gojimmypi/ulx3s-elecrow-7inch-hdmi-enclosure/images/A1-A1-connector-size.jpg

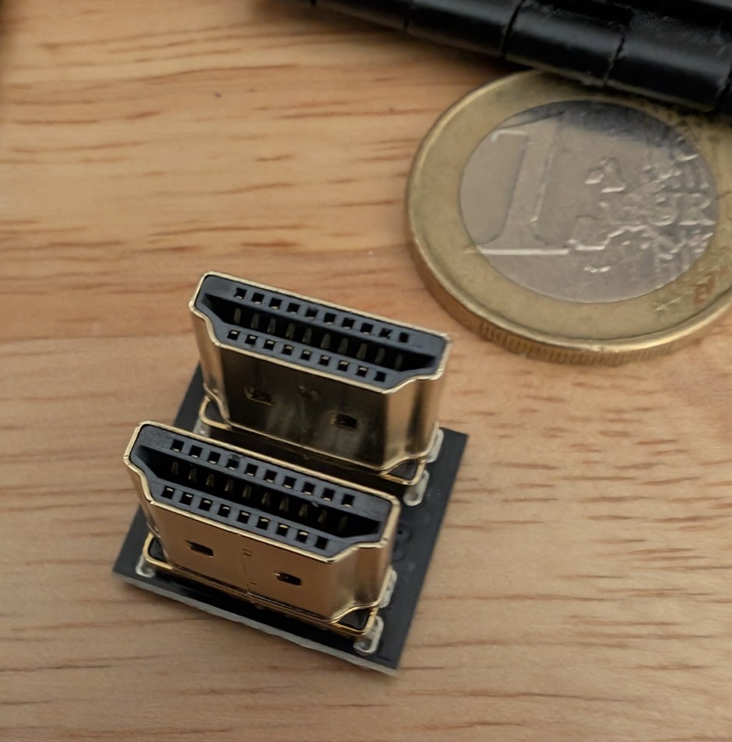
images/A1-A1-connector-size.jpg
