gojimmypi/ulx3s-elecrow-7inch-hdmi-enclosure/images/creality_filament_tangle.jpg

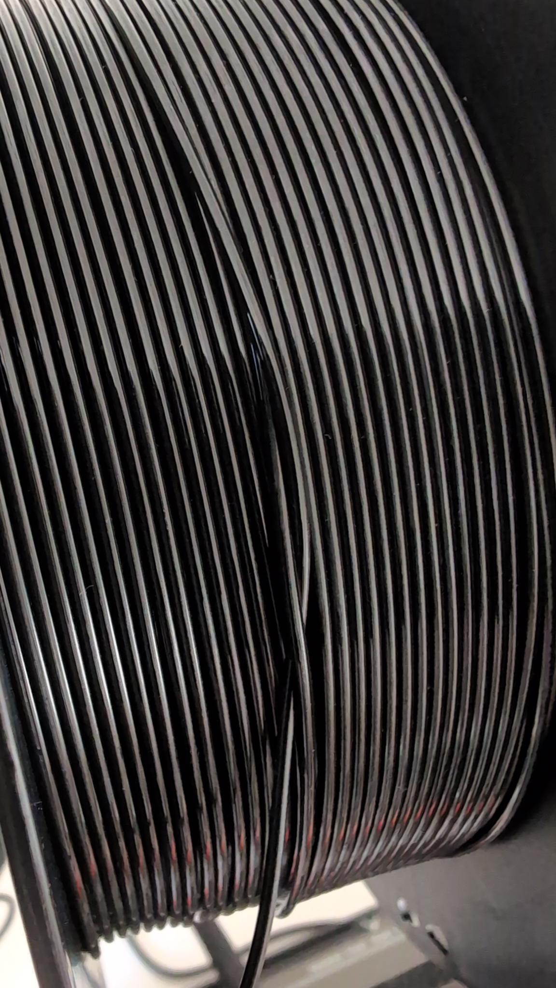
images/creality_filament_tangle.jpg
