gojimmypi/ulx3s-elecrow-7inch-hdmi-enclosure/images/creality_support_reply.jpg

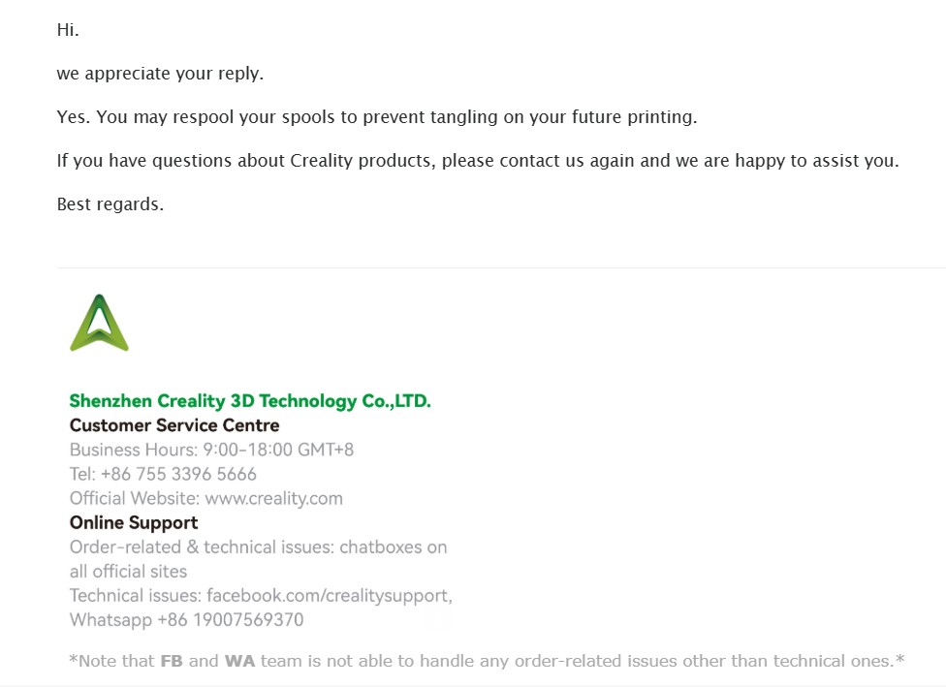
images/creality_support_reply.jpg
