gojimmypi/ulx3s-elecrow-7inch-hdmi-enclosure/images/Elecrow-7inch-HMDI-dimensions.jpg

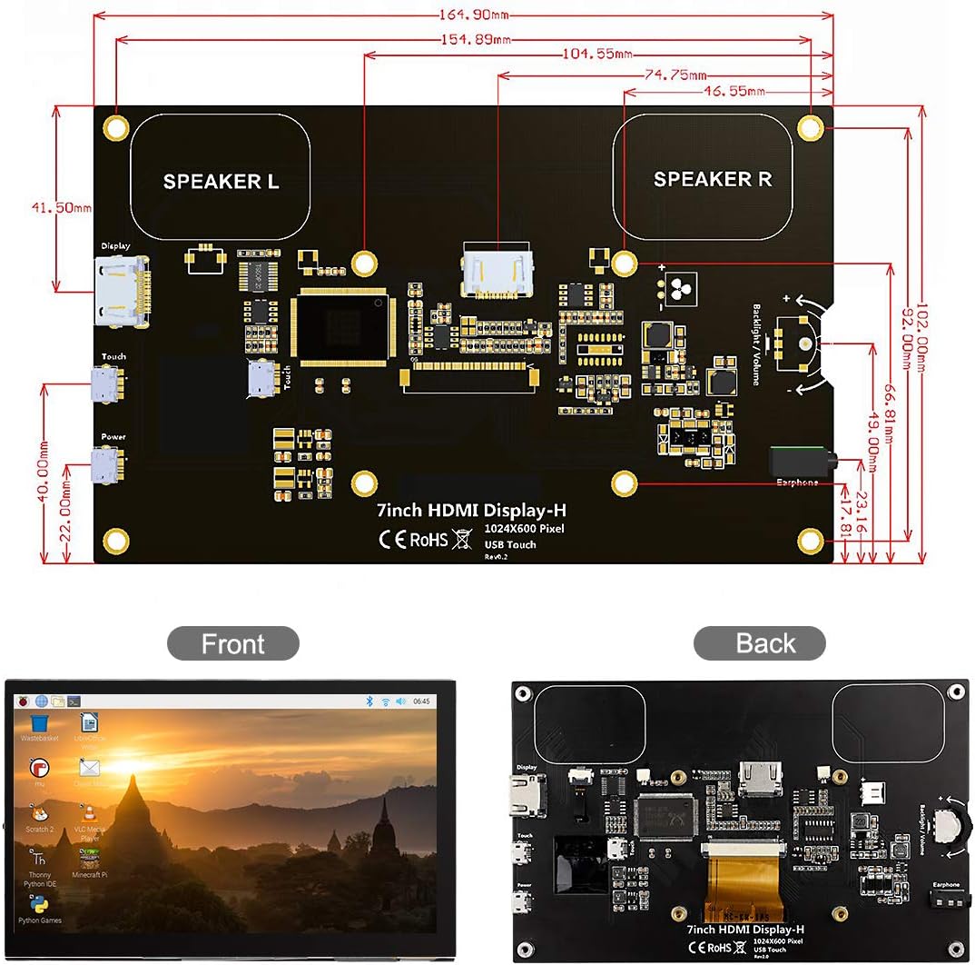
images/Elecrow-7inch-HMDI-dimensions.jpg
