gojimmypi/ulx3s-elecrow-7inch-hdmi-enclosure/images/Elecrow-HDMI-stubout.jpg

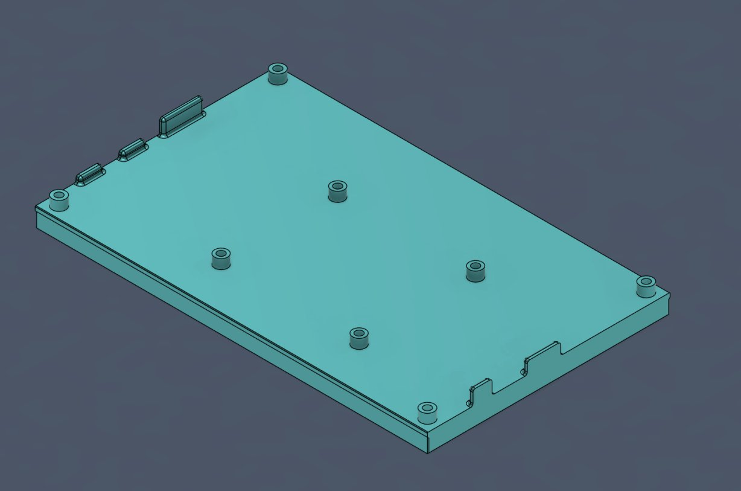
images/Elecrow-HDMI-stubout.jpg
