gojimmypi/ulx3s-elecrow-7inch-hdmi-enclosure/images/Enclosure-with-display-stubout-front.jpg

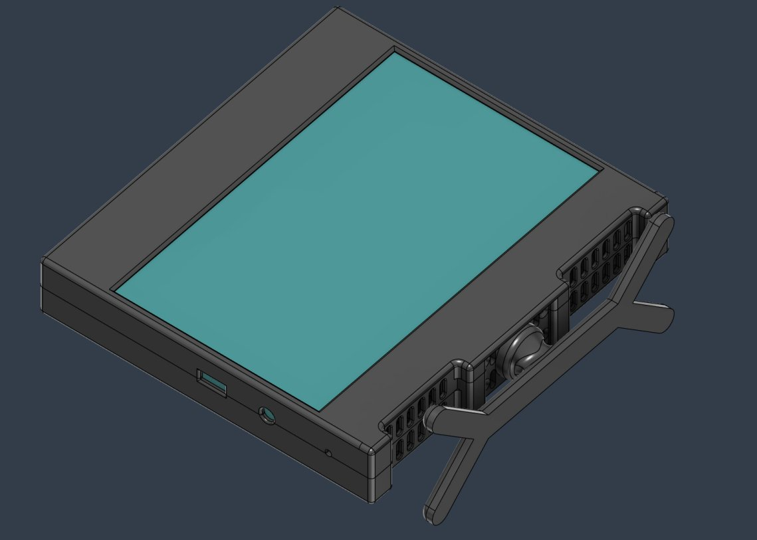
images/Enclosure-with-display-stubout-front.jpg
