gojimmypi/ulx3s-elecrow-7inch-hdmi-enclosure/images/Enclosure-with-display-stubout-rear.jpg

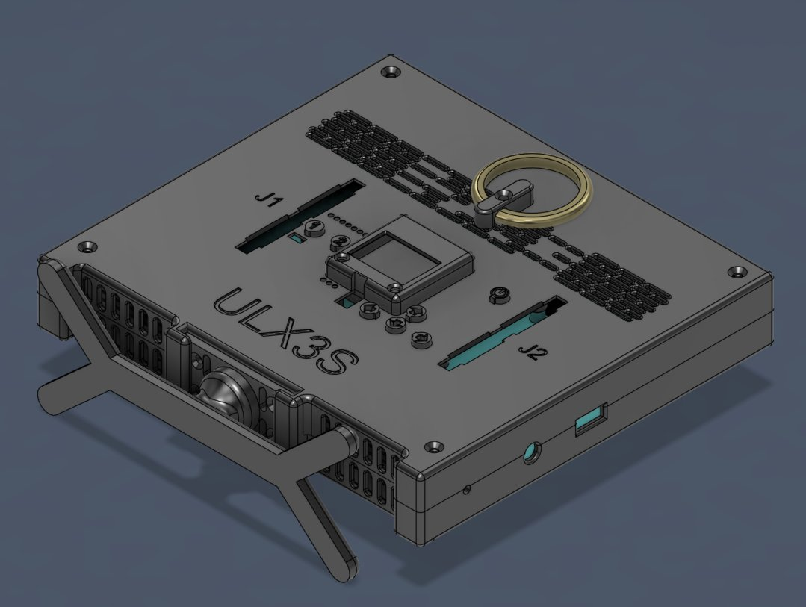
images/Enclosure-with-display-stubout-rear.jpg
