gojimmypi/ulx3s-elecrow-7inch-hdmi-enclosure/images/enclosure_display_side.jpg

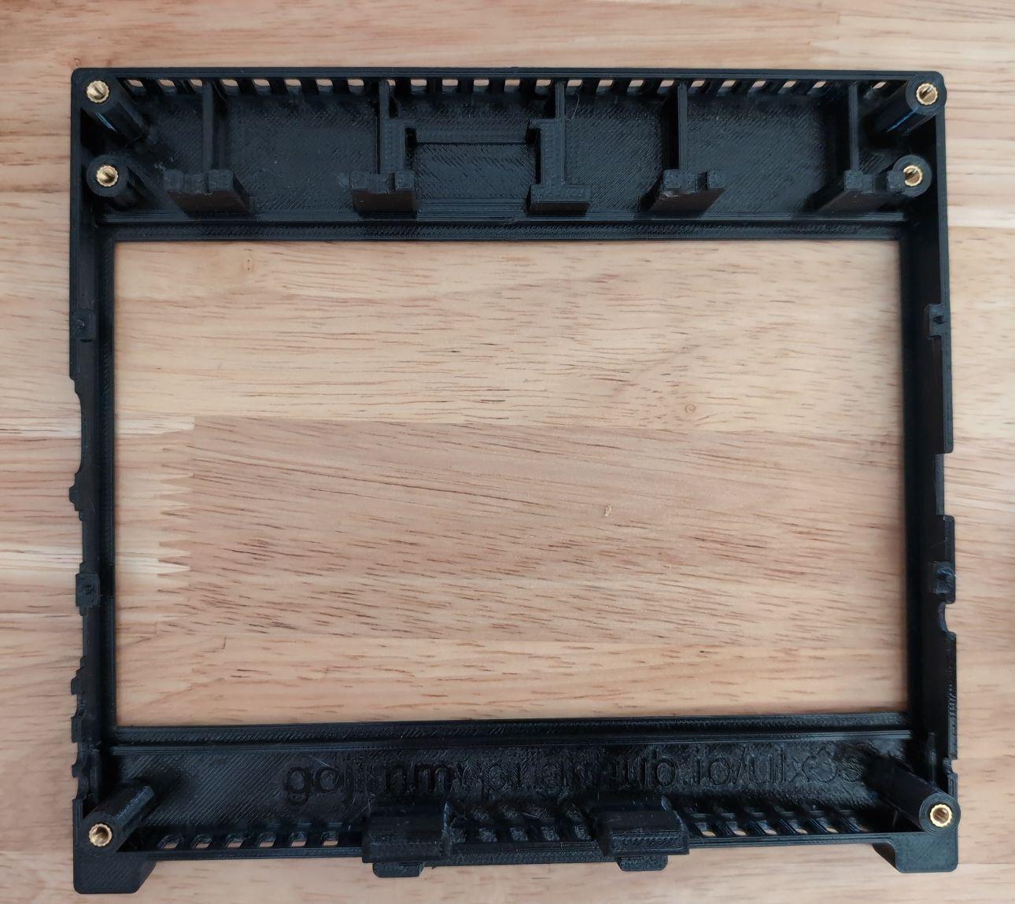
images/enclosure_display_side.jpg
