gojimmypi/ulx3s-elecrow-7inch-hdmi-enclosure/images/enclosure_render_display_side.jpg

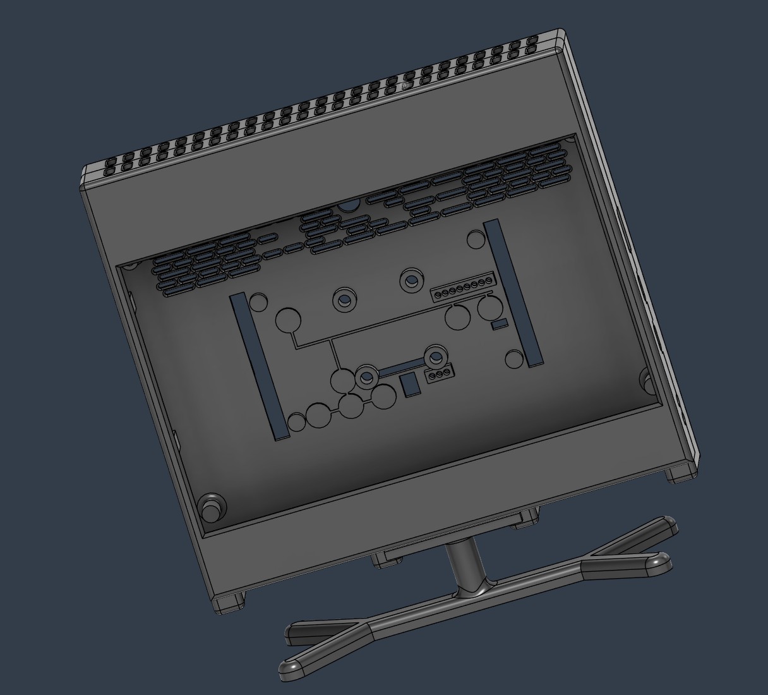
images/enclosure_render_display_side.jpg
