gojimmypi/ulx3s-elecrow-7inch-hdmi-enclosure/images/error.jpg

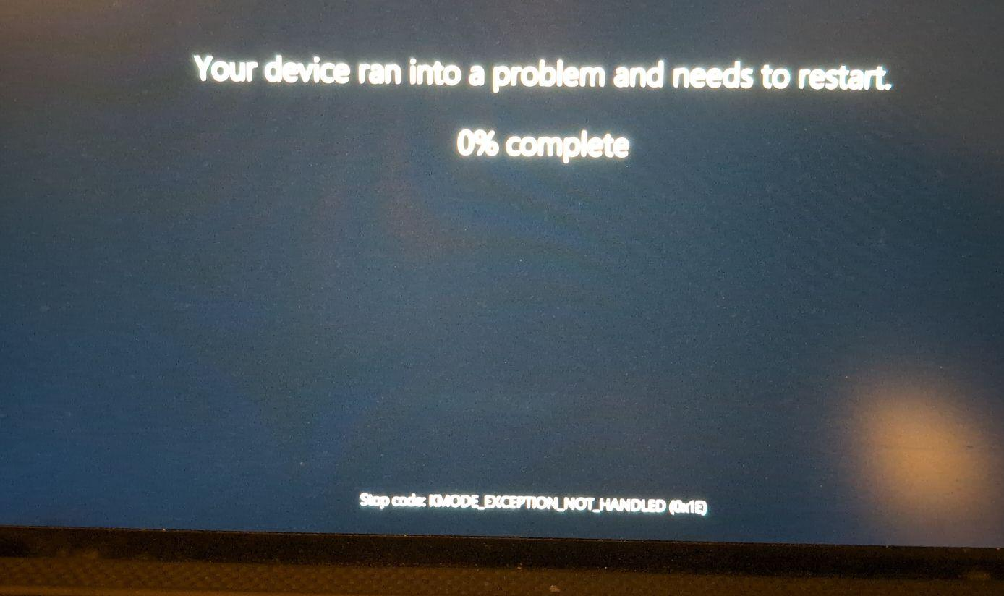
images/error.jpg
