gojimmypi/ulx3s-elecrow-7inch-hdmi-enclosure/images/fan_25mm.jpg

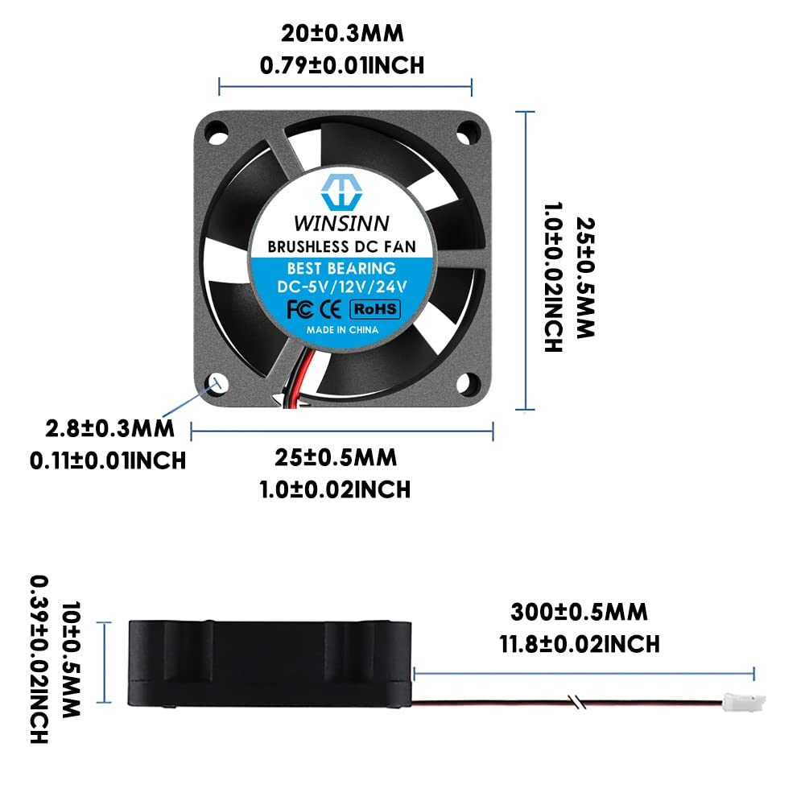
images/fan_25mm.jpg
