gojimmypi/ulx3s-elecrow-7inch-hdmi-enclosure/images/hdmi adapter on display.jpg

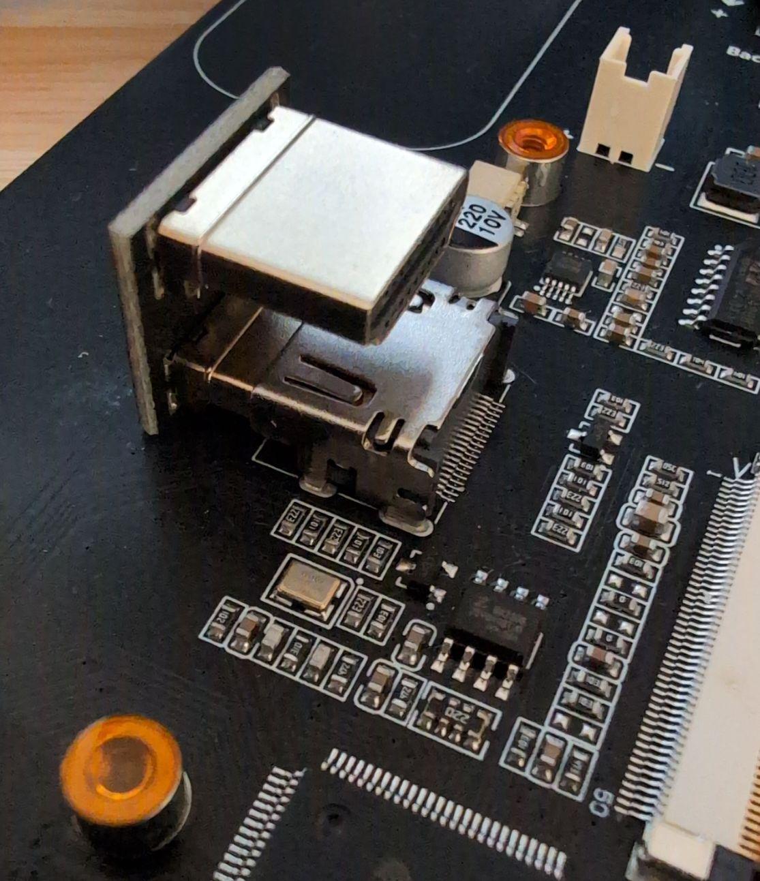
images/hdmi adapter on display.jpg
