gojimmypi/ulx3s-elecrow-7inch-hdmi-enclosure/images/HDMI bracket with ULX3S.jpg

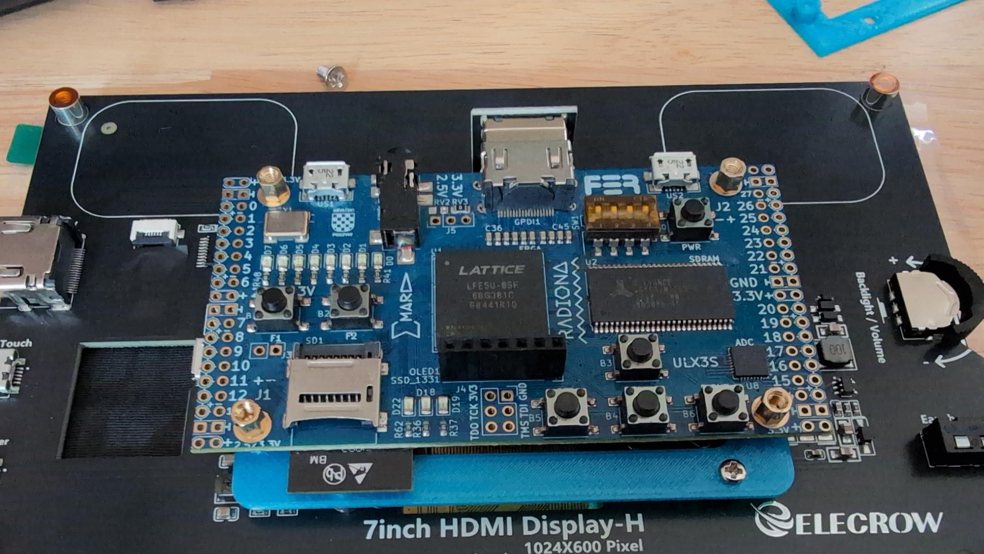
images/HDMI bracket with ULX3S.jpg
