gojimmypi/ulx3s-elecrow-7inch-hdmi-enclosure/images/HDMI bracket.jpg

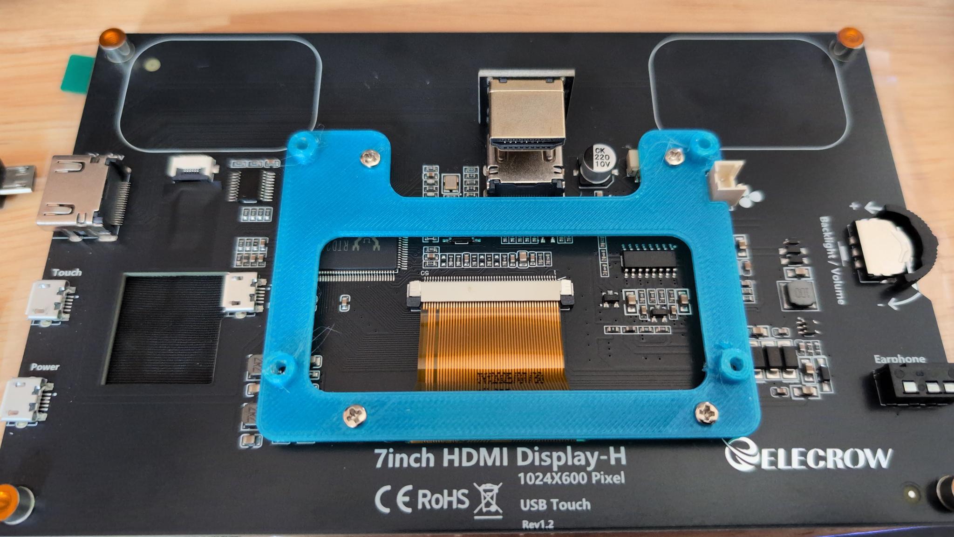
images/HDMI bracket.jpg
