gojimmypi/ulx3s-elecrow-7inch-hdmi-enclosure/images/HDMI-A1-Options.jpg

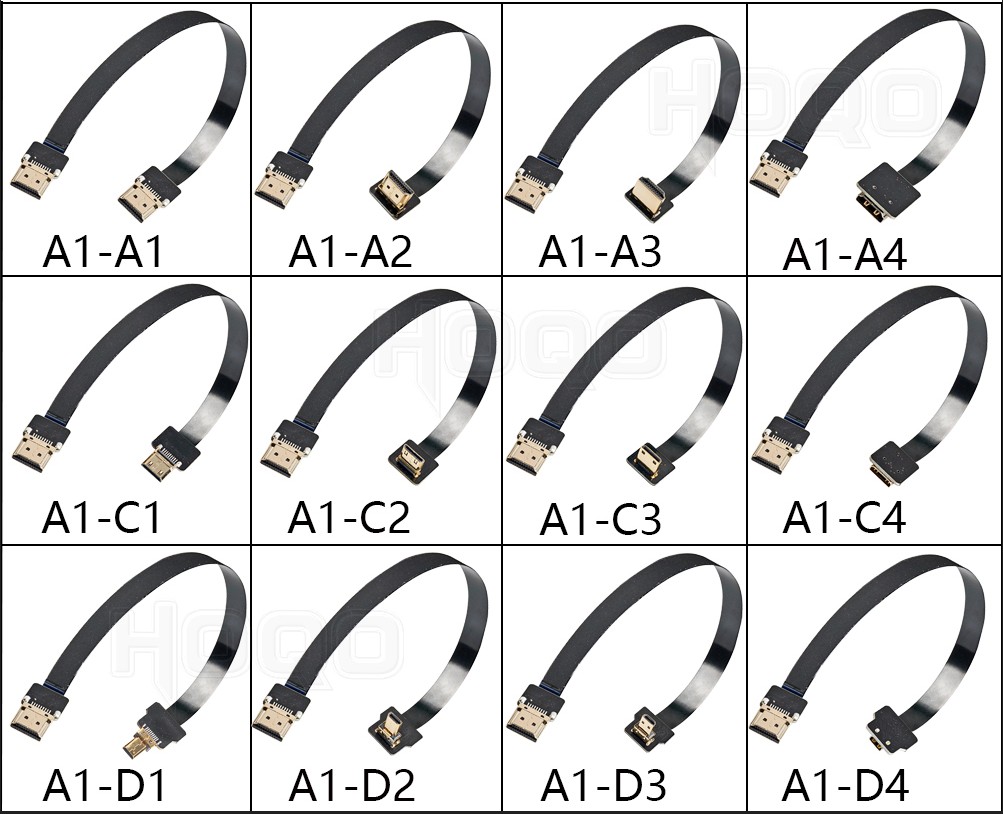
images/HDMI-A1-Options.jpg
