gojimmypi/ulx3s-elecrow-7inch-hdmi-enclosure/images/HDMI_USB-stubout-analysis-view.jpg

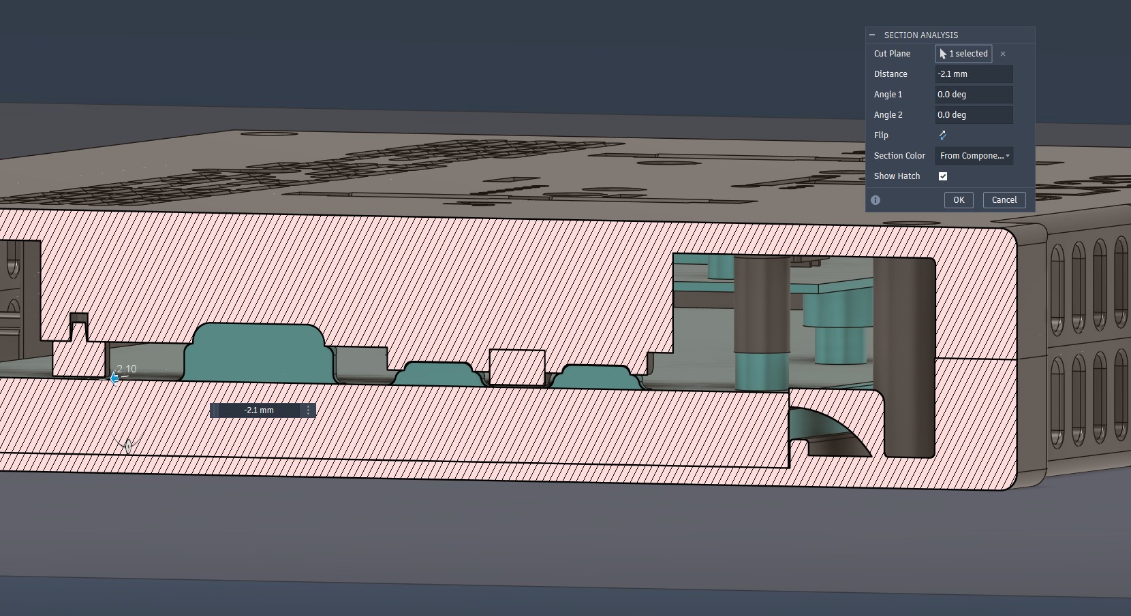
images/HDMI_USB-stubout-analysis-view.jpg
