gojimmypi/ulx3s-elecrow-7inch-hdmi-enclosure/images/keyhole-to-lanyard-adapter.jpg

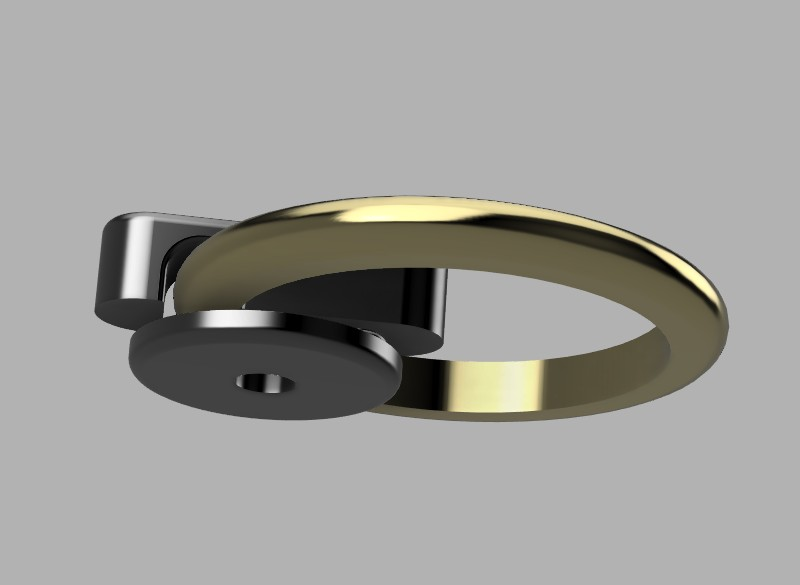
images/keyhole-to-lanyard-adapter.jpg
