gojimmypi/ulx3s-elecrow-7inch-hdmi-enclosure/images/SSD_1331_OLED_Display.jpg

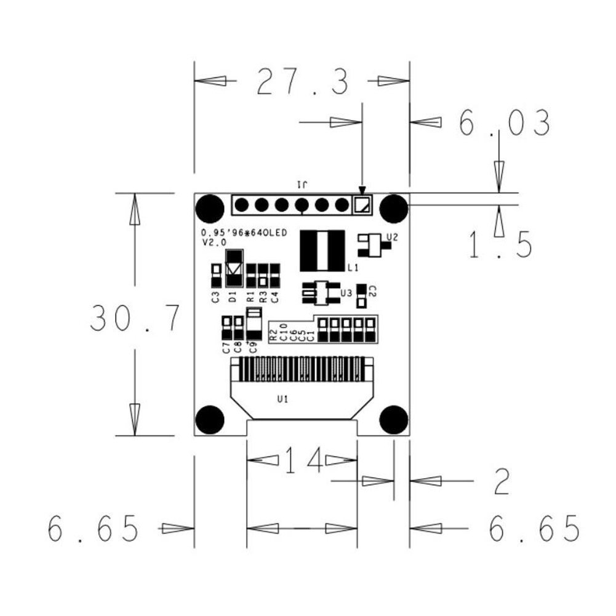
images/SSD_1331_OLED_Display.jpg
