gojimmypi/ulx3s-elecrow-7inch-hdmi-enclosure/images/steel-rendering.jpg

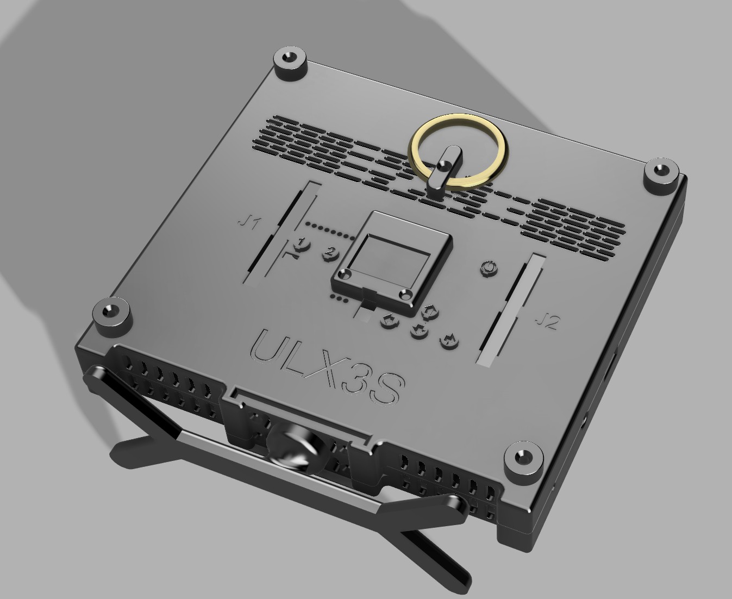
images/steel-rendering.jpg
