gojimmypi/ulx3s-elecrow-7inch-hdmi-enclosure/images/ULX3S Bracket.PNG

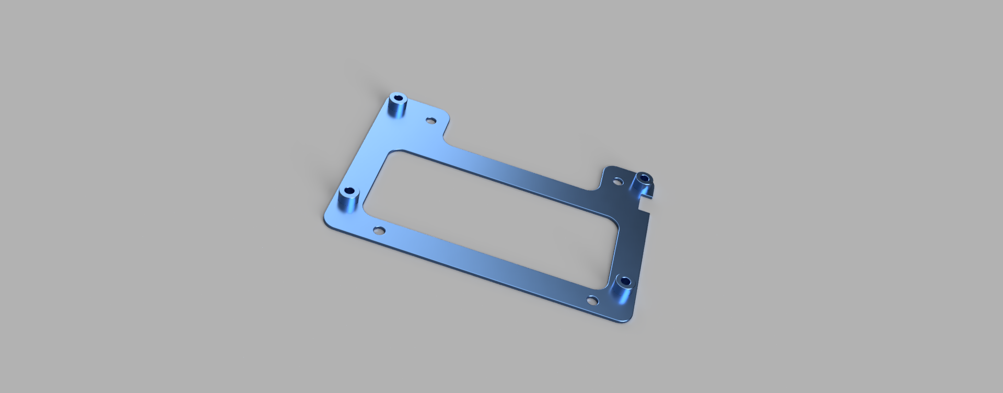
images/ULX3S Bracket.PNG
