gojimmypi/ulx3s-elecrow-7inch-hdmi-enclosure/images/ULX3S HDMI plug 1.jpg

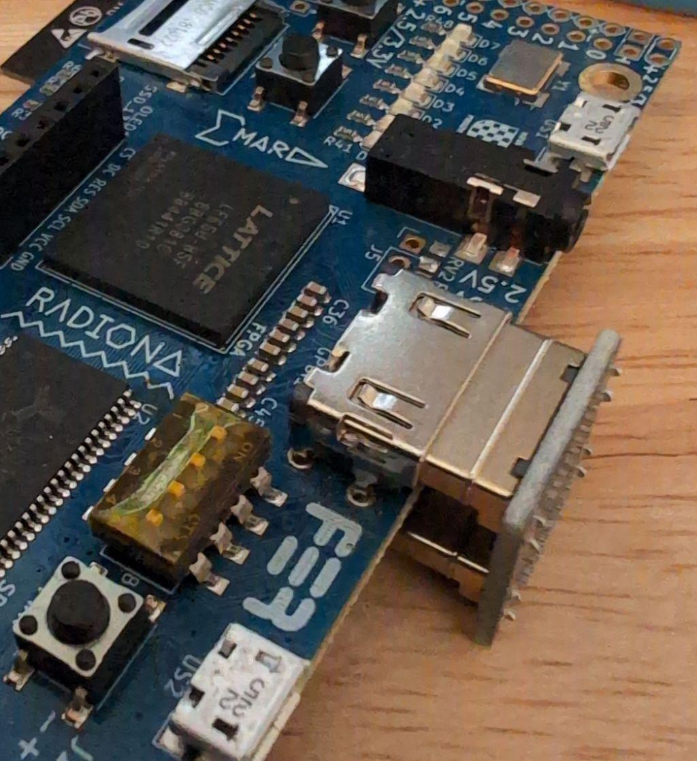
images/ULX3S HDMI plug 1.jpg
