gojimmypi/ulx3s-elecrow-7inch-hdmi-enclosure/images/ULX3S HDMI plug 2.jpg

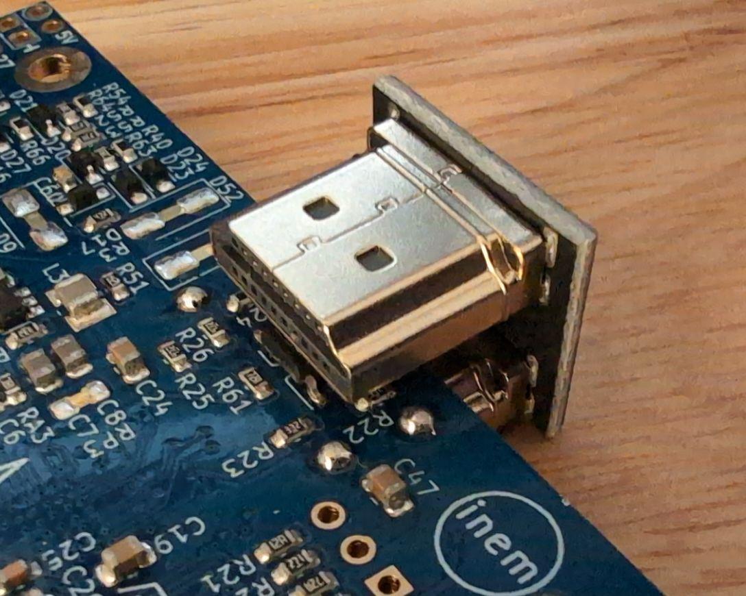
images/ULX3S HDMI plug 2.jpg
