gojimmypi/ulx3s-elecrow-7inch-hdmi-enclosure/images/USB_Routing.jpg

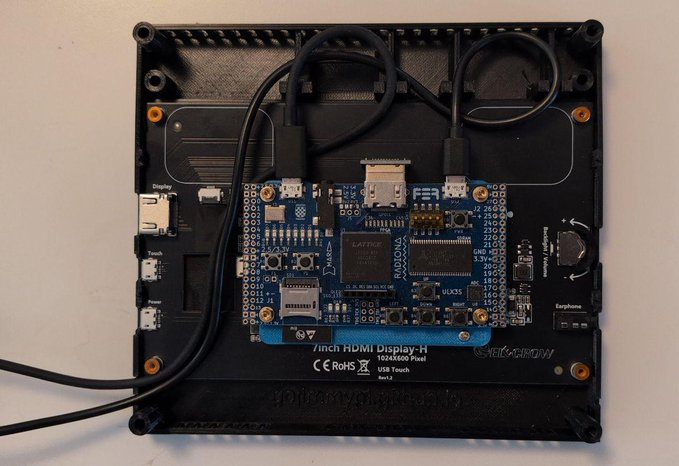
images/USB_Routing.jpg
