gojimmypi/ulx3s-elecrow-7inch-hdmi-enclosure/STL/OLED Frame.stl

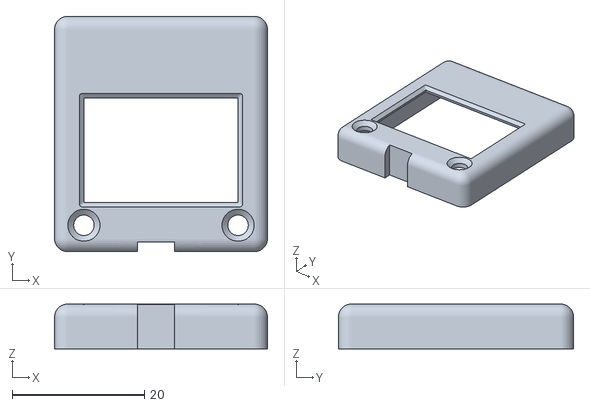
[picture p49: CAD file, 2026-03-18]
STL/OLED Frame.stl
32.2 x 35.6 x 6.80
