gojimmypi/ulx3s-elecrow-7inch-hdmi-enclosure/Prusa/Button Set.3mf

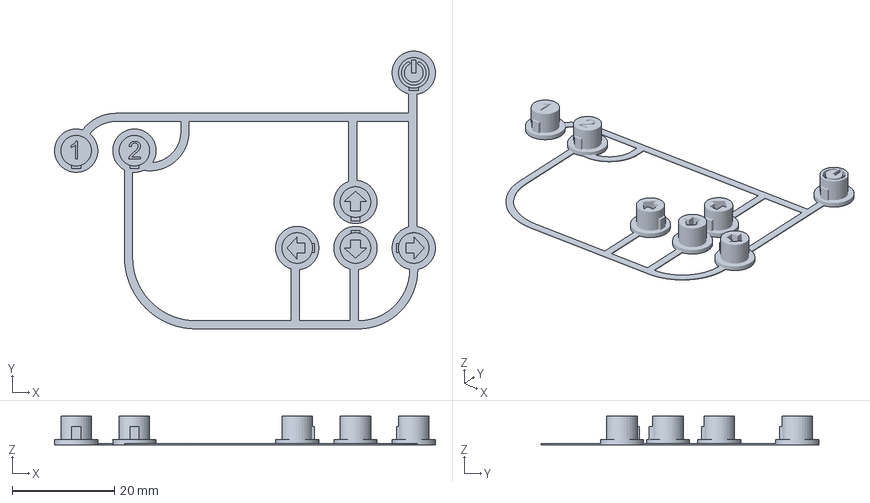
[picture p50: CAD file, 2026-03-20]
Prusa/Button Set.3mf
74.5 x 54.4 x 5.60 mm
