gojimmypi/ulx3s-elecrow-7inch-hdmi-enclosure/STL/Rear Foot.stl

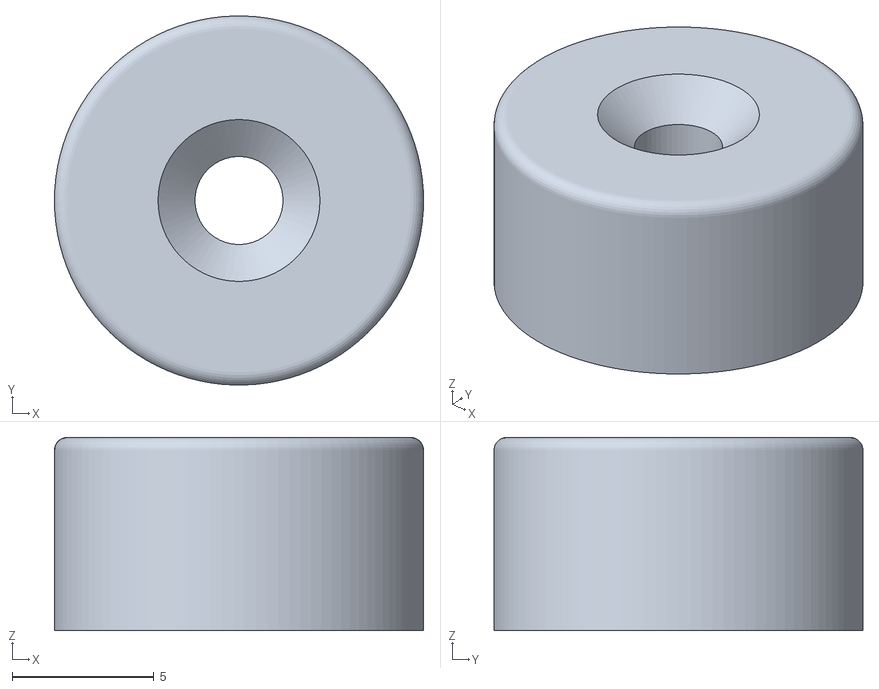
[picture p51: CAD file, 2026-03-18]
STL/Rear Foot.stl
13.0 x 13.0 x 6.80
