gojimmypi/ulx3s-elecrow-7inch-hdmi-enclosure/Prusa/Keyhole External Adapter.3mf

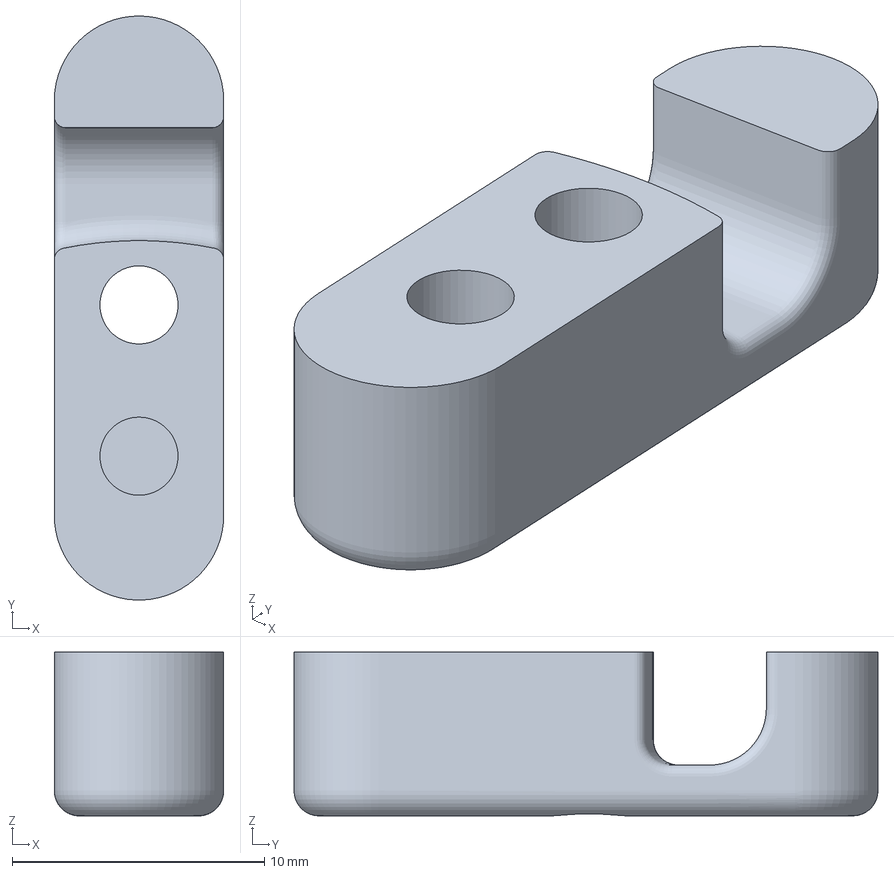
[picture p52: CAD file, 2026-03-20]
Prusa/Keyhole External Adapter.3mf
6.72 x 23.2 x 6.50 mm
