gojimmypi/ulx3s-elecrow-7inch-hdmi-enclosure/Prusa/Keychain Ring Mockup.3mf

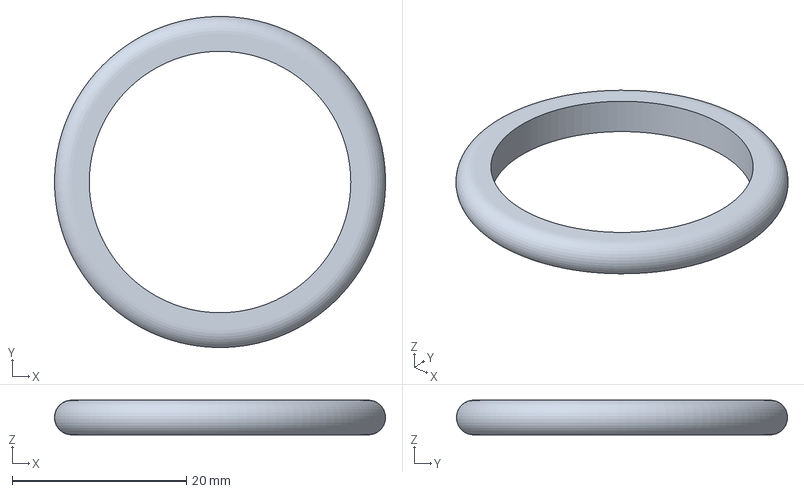
[picture p53: CAD file, 2026-03-20]
Prusa/Keychain Ring Mockup.3mf
38.0 x 38.0 x 4.00 mm
