gojimmypi/ulx3s-elecrow-7inch-hdmi-enclosure/STL/J3 Cover.stl

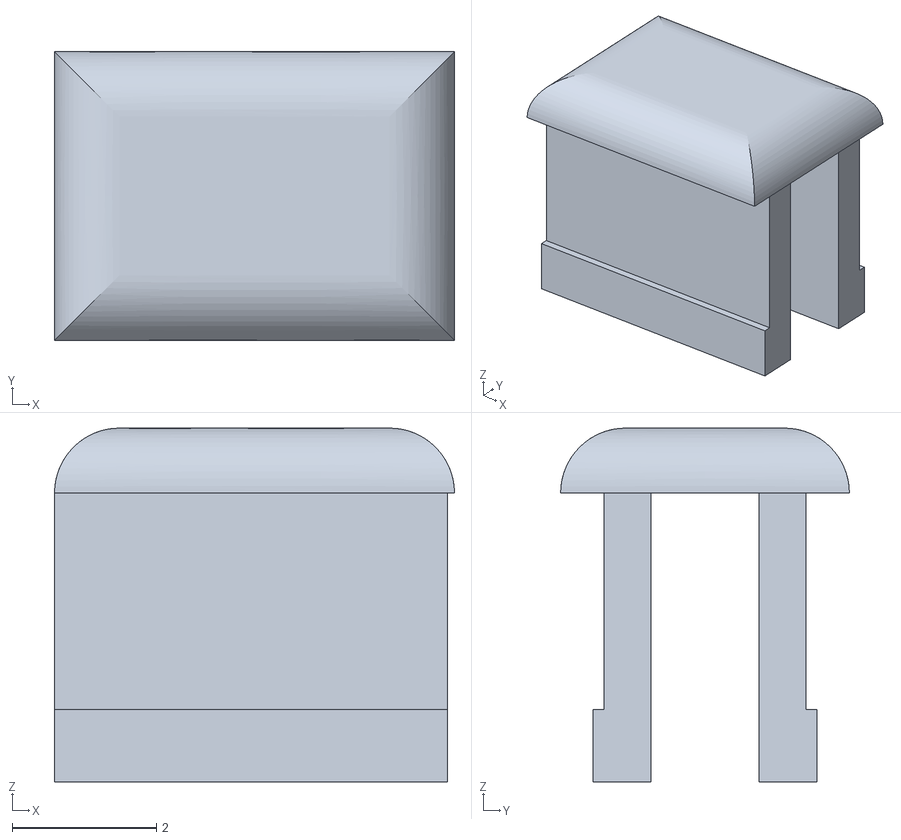
[picture p54: CAD file, 2026-03-18]
STL/J3 Cover.stl
5.54 x 4.00 x 4.90
