gojimmypi/ulx3s-elecrow-7inch-hdmi-enclosure/Prusa/Adapter Base Plate Spacer  2.3mf

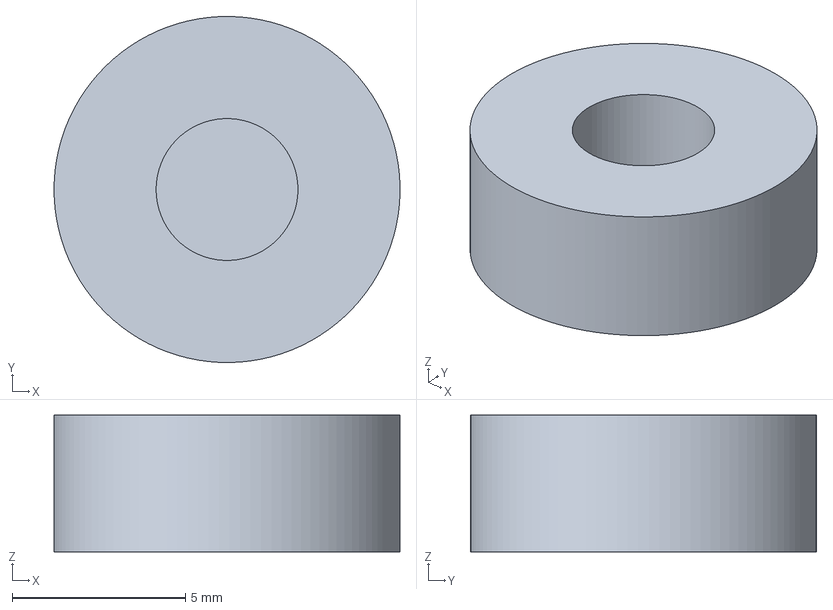
[picture p55: CAD file, 2026-03-20]
Prusa/Adapter Base Plate Spacer 2.3mf
10.00 x 10.00 x 3.95 mm
