gojimmypi/ulx3s-elecrow-7inch-hdmi-enclosure/STL/USB Restraint Cap.stl

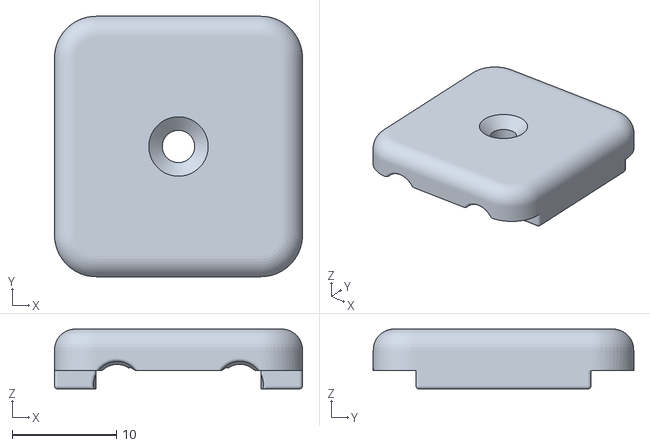
[picture p56: CAD file, 2026-03-18]
STL/USB Restraint Cap.stl
23.8 x 25.0 x 5.75
