gojimmypi/ulx3s-elecrow-7inch-hdmi-enclosure/STL/Keyhole Face Insert.stl

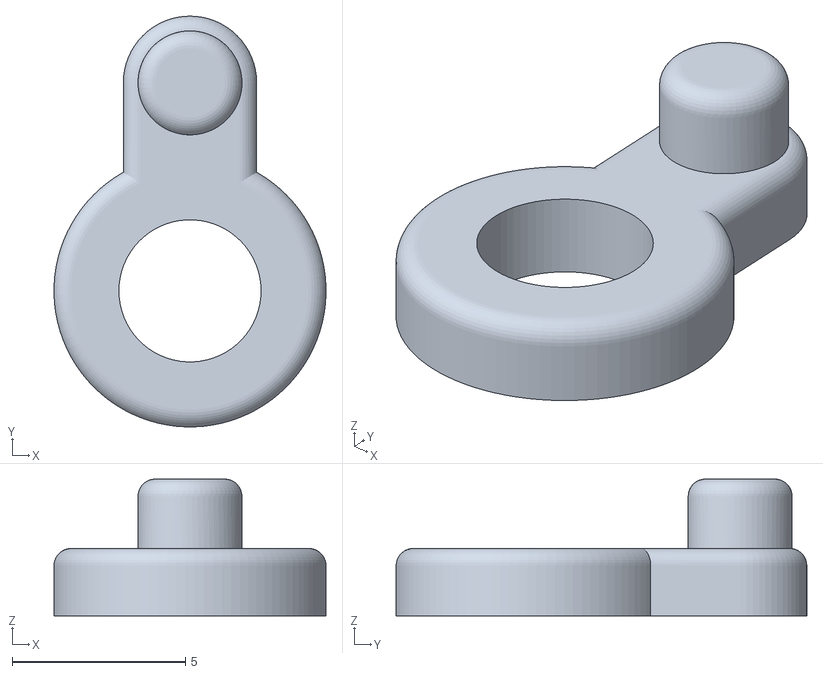
[picture p57: CAD file, 2026-03-18]
STL/Keyhole Face Insert.stl
7.85 x 11.8 x 3.95
