gojimmypi/ulx3s-elecrow-7inch-hdmi-enclosure/Prusa/ULX3S Face Covers.3mf

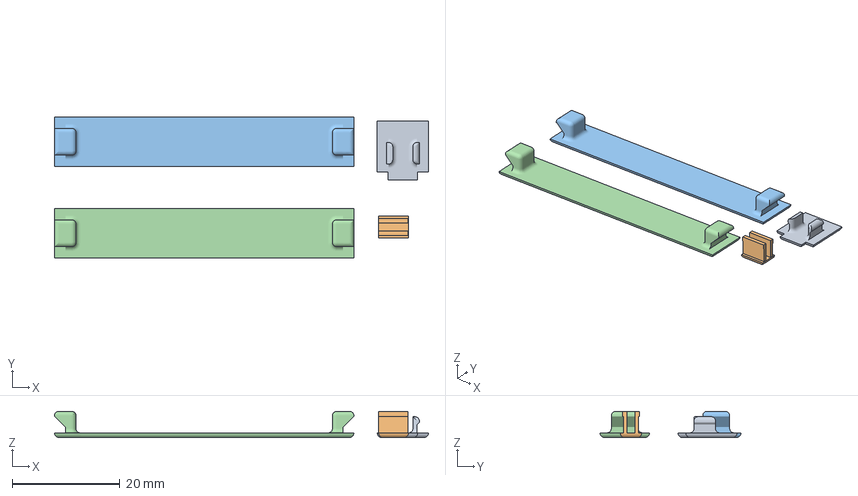
[picture p58: CAD file, 2026-03-20]
Prusa/ULX3S Face Covers.3mf
69.5 x 26.2 x 4.90 mm
J4 Cover.stl
J3 Cover.stl
J2 Cover.stl
J1 Cover.stl
