gojimmypi/ulx3s-elecrow-7inch-hdmi-enclosure/STL/J4 Cover.stl

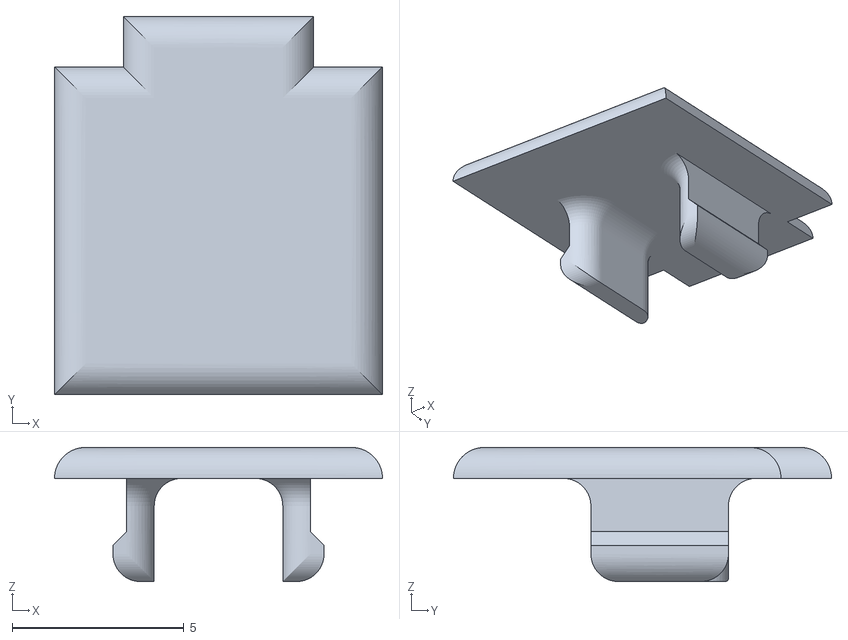
[picture p59: CAD file, 2026-03-18]
STL/J4 Cover.stl
9.54 x 11.0 x 3.90
