gojimmypi/ulx3s-elecrow-7inch-hdmi-enclosure/Prusa/Adapter Base Plate.3mf

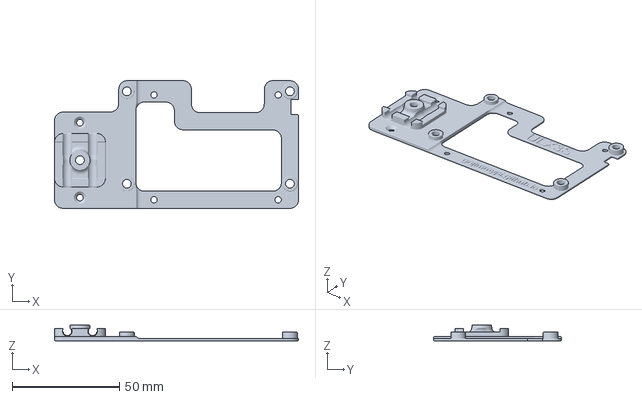
[picture p60: CAD file, 2026-03-20]
Prusa/Adapter Base Plate.3mf
114.0 x 59.7 x 7.25 mm
