gojimmypi/ulx3s-elecrow-7inch-hdmi-enclosure/Prusa/J2 Cover.3mf

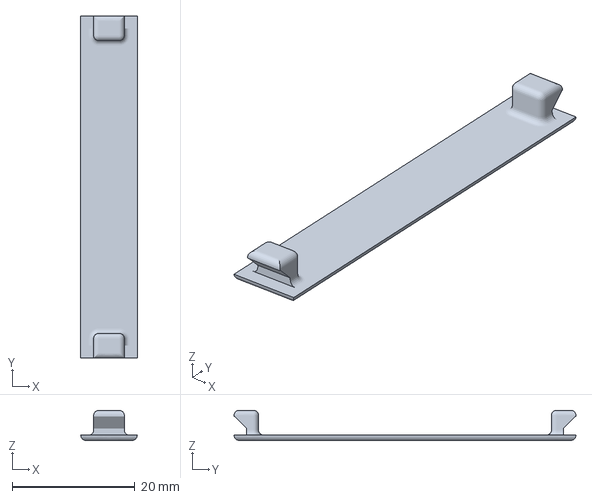
[picture p61: CAD file, 2026-03-20]
Prusa/J2 Cover.3mf
9.20 x 55.7 x 4.90 mm
