gojimmypi/ulx3s-elecrow-7inch-hdmi-enclosure/STL/Light Pipe Sample.stl

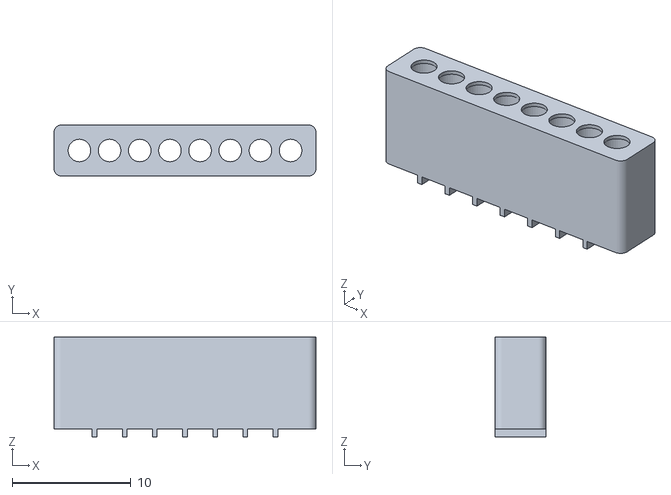
[picture p62: CAD file, 2026-03-18]
STL/Light Pipe Sample.stl
22.1 x 4.28 x 8.40
