gojimmypi/ulx3s-elecrow-7inch-hdmi-enclosure/STL/Stand.stl

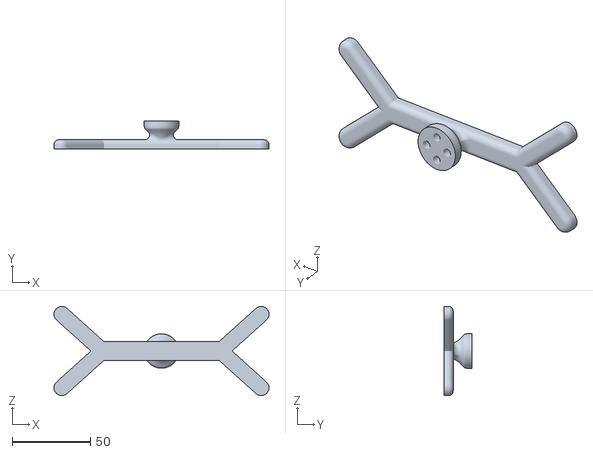
[picture p63: CAD file, 2026-03-18]
STL/Stand.stl
137.0 x 18.1 x 56.8
