gojimmypi/ulx3s-elecrow-7inch-hdmi-enclosure/Prusa/Adapter Base Plate Set.3mf

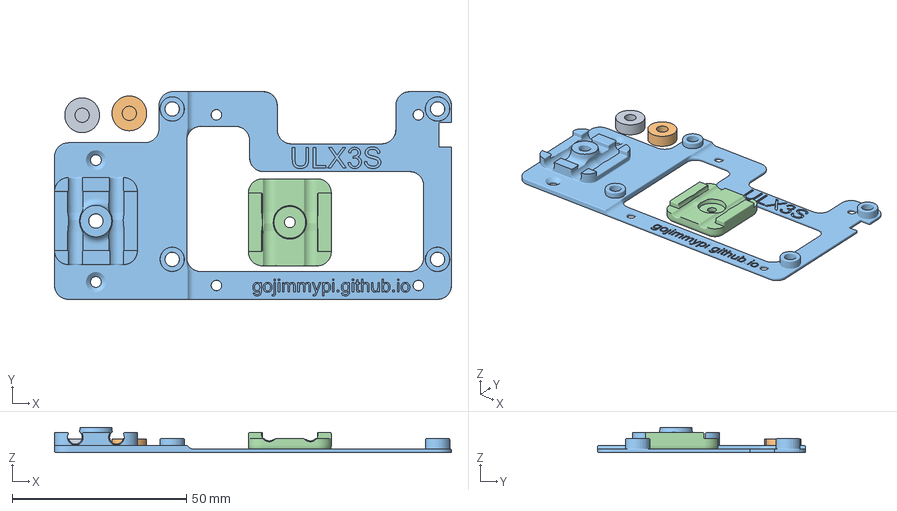
[picture p64: CAD file, 2026-03-20]
Prusa/Adapter Base Plate Set.3mf
114.0 x 59.7 x 7.25 mm
Adapter Base Plate Spacer.stl
Adapter Base Plate Spacer 2.stl
Adapter Base Plate.stl
USB Restraint Cap.stl
