gojimmypi/ulx3s-elecrow-7inch-hdmi-enclosure/STL/Stand Mounting Plate.stl

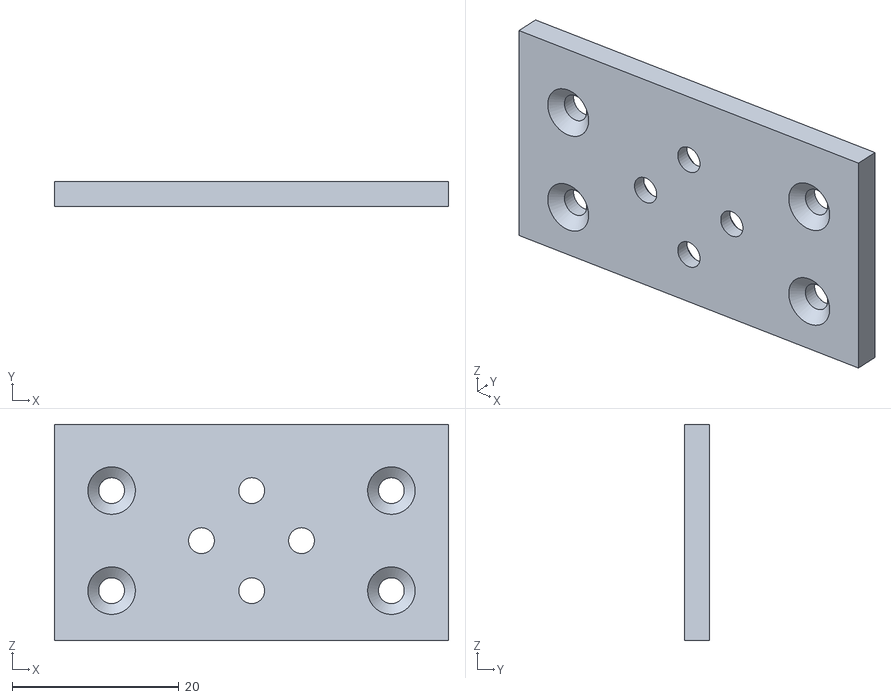
[picture p65: CAD file, 2026-03-18]
STL/Stand Mounting Plate.stl
47.2 x 2.95 x 25.9
