gojimmypi/ulx3s-elecrow-7inch-hdmi-enclosure/STL/ULX3S Mockup.stl

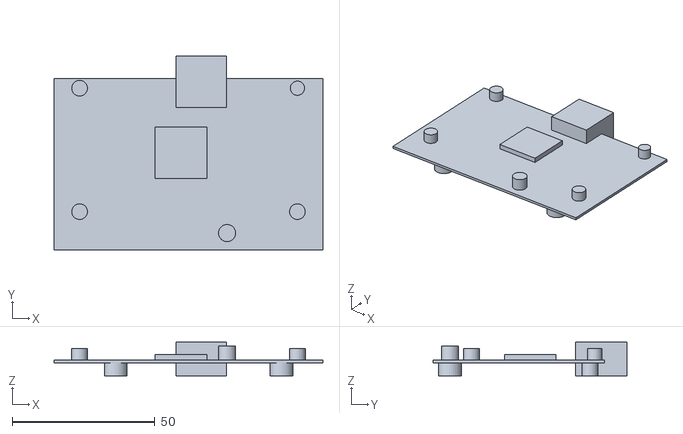
[picture p66: CAD file, 2026-03-18]
STL/ULX3S Mockup.stl
94.1 x 68.0 x 11.8
