gojimmypi/ulx3s-elecrow-7inch-hdmi-enclosure/Prusa/Stand Mounting Plate.3mf

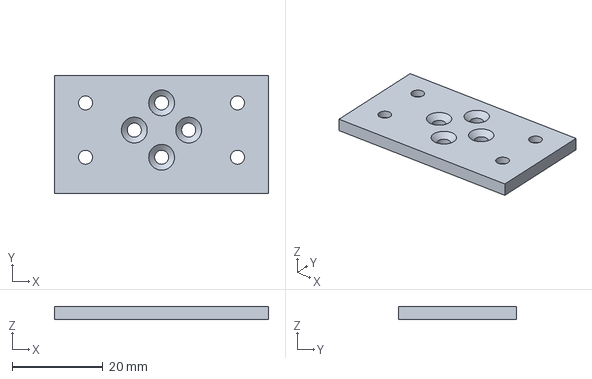
[picture p67: CAD file, 2026-03-20]
Prusa/Stand Mounting Plate.3mf
47.2 x 26.0 x 2.95 mm
